smart-fun/elastick/resources/joysticks/amiga_joystick.jpg

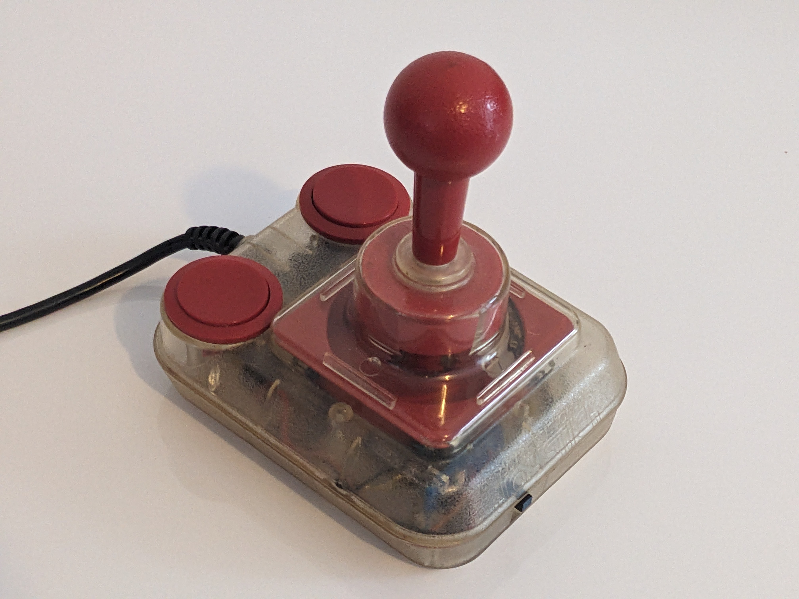
resources/joysticks/amiga_joystick.jpg
