smart-fun/elastick/resources/joysticks/atari_2600_paddles.jpg

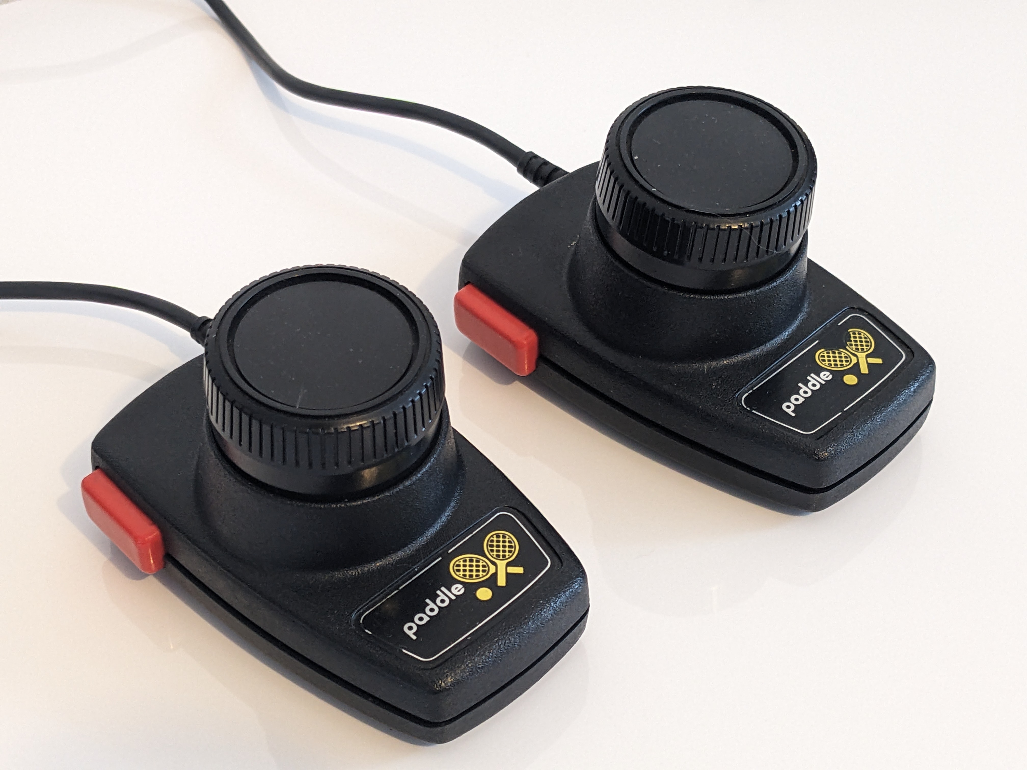
resources/joysticks/atari_2600_paddles.jpg
