smart-fun/elastick/resources/joysticks/coco_deluxe_joystick.jpg

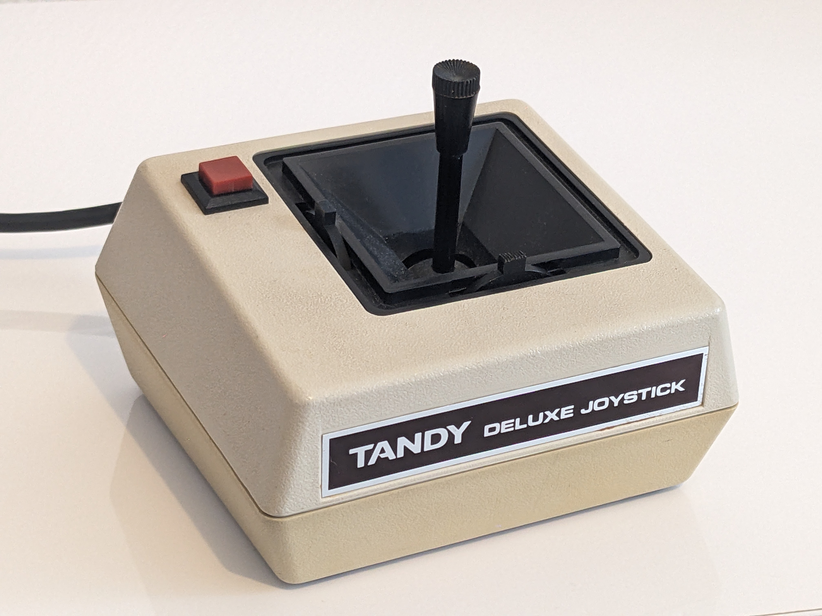
resources/joysticks/coco_deluxe_joystick.jpg
