smart-fun/elastick/resources/joysticks/mega_drive_control_pad.jpg

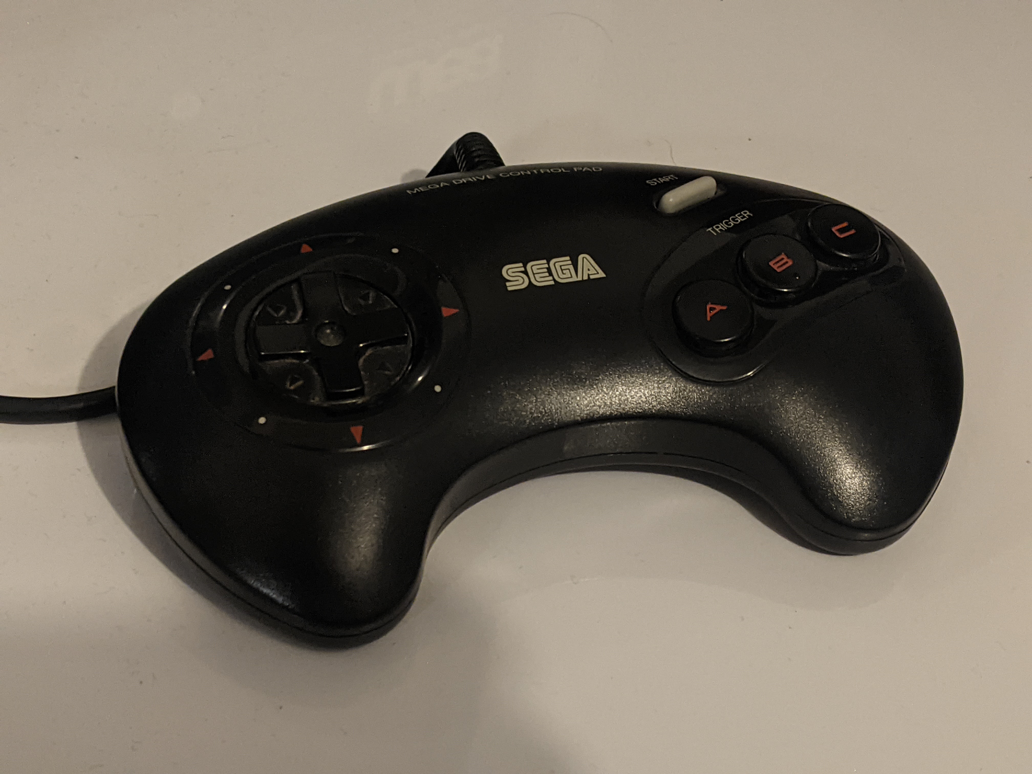
resources/joysticks/mega_drive_control_pad.jpg
