smart-fun/elastick/code/elastick/src/controllers/mega_drive_controller.h

#pragma once
#include "game_controller.h"

class MegaDriveController : public DigitalGameController {
public:
    MegaDriveController();
    uint8_t getNbButtons() override { return 4; };
    void init() override;
    void update() override;
    bool initDetection() override { return false; };
    float readAxis(uint8_t axisNumber) override;
    uint8_t readButton(uint8_t buttonNumber) override;
private:
    std::vector<PinConfig> mappingARules;
    std::vector<PinConfig> mappingBRules;
    bool buttonUp = false;
    bool buttonDown = false;
    bool buttonLeft = false;
    bool buttonRight = false;
    bool buttonA = false;
    bool buttonB = false;
    bool buttonC = false;
    bool buttonStart = false;
};
