smart-fun/elastick/code/elastick/src/menus/ControllersMenu.h

#pragma once

#include "ListMenu.h"
#include "ControllerCategory.h"

class ControllersMenu : public ListMenu {
public:
    ControllersMenu(ControllerCategory controllerCategory);
private:
    ControllerCategory controllerCategory;
};
