smart-fun/elastick/code/elastick/src/controllers/atari_mouse_controller.h

#pragma once
#include "mouse_controller.h"

class AtariMouseController : public MouseController {
public:
    AtariMouseController();
    void init() override;
    void deinit() override;
    void update() override;
protected:
    void getMouseDirectionPins(uint8_t &x1Pin, uint8_t &x2Pin, uint8_t &y1Pin, uint8_t &y2Pin) override;
    void getMouseButtonPins(uint8_t &button1Pin, uint8_t &button2Pin, uint8_t &button3Pin) override;
};
