smart-fun/elastick/code/elastick/src/menus/ListMenu.cpp

#include "ListMenu.h"
#include "DisplayManager.h"
#include "game_controllers.h"
#include "MenuController.h"

MenuItem::MenuItem(MenuItemType type, const char *displayText)
{
    this->type = type;
    this->displayText = displayText;
}

MenuItem::MenuItem(MenuAction menuAction, const char *displayText)
    : MenuItem(MenuItemType::Action, displayText)
{
    data.menuAction = menuAction;
}

MenuItem::MenuItem(ControllerCategory controllerCategory, const char *displayText)
    : MenuItem(MenuItemType::Category, displayText)
{
    data.controllerCategory = controllerCategory;
}

MenuItem::MenuItem(GameController *controller, const char *displayText)
    : MenuItem(MenuItemType::Controller, displayText)
{
    data.controller = controller;
}

ListMenu::ListMenu()
{
}

void ListMenu::show()
{
    DisplayManager::getInstance().showList(getTitle(), list, selectedIndex);
}

void ListMenu::update()
{
    // nothing to do so far
}

void ListMenu::onPrevious()
{
    if (selectedIndex > 0)
    {
        --selectedIndex;
    }
    show();
}

void ListMenu::onNext()
{
    if (selectedIndex < list.size() - 1)
    {
        ++selectedIndex;
    }
    show();
}

// TODO: call controller->deinit() when going back to Joystick/Mouse/Paddle Menus (from Test or Play)
void ListMenu::onValidate()
{
    MenuItem *menuItem = list[selectedIndex];
    switch (menuItem->type)
    {
    case MenuItemType::Action:
    {
        MenuAction menuAction = menuItem->data.menuAction;
        if (menuAction == MenuAction::BACK_TO_CATEGORY_MENU)
        {
            MenuController::getInstance().setCurrentMenu(MenuController::MenuID::Category);
        }
        else if (menuAction == MenuAction::BACK_TO_CONTROLLERS_MENU)
        {
            GameController *controller = GameControllers::getInstance().getSelectedController();
            controller->deinit();
            ControllerCategory category = controller->getCategory();
            startControllersMenu(category);
        }
        else if (menuAction == MenuAction::PLAY)
        {
            GameController *controller = GameControllers::getInstance().getSelectedController();
            controller->init();
            MenuController::getInstance().setCurrentMenu(MenuController::MenuID::Play);
        }
        else if (menuAction == MenuAction::TEST)
        {
            GameController *controller = GameControllers::getInstance().getSelectedController();
            controller->init();
            MenuController::getInstance().setCurrentMenu(MenuController::MenuID::Test);
        }
        break;
    }
    case MenuItemType::Category:
    {
        startControllersMenu(menuItem->data.controllerCategory);
        break;
    }
    case MenuItemType::Controller:
    {
        GameController *controller = menuItem->data.controller;
        GameControllers::getInstance().setSelectedController(controller);
        // selected->init();
        MenuController::getInstance().setCurrentMenu(MenuController::MenuID::Action);
        break;
    }
    }
}

void ListMenu::startControllersMenu(ControllerCategory category)
{
    if (category == ControllerCategory::JOY)
    {
        MenuController::getInstance().setCurrentMenu(MenuController::MenuID::JoystickList);
    }
    else if (category == ControllerCategory::MOUSE)
    {
        MenuController::getInstance().setCurrentMenu(MenuController::MenuID::MouseList);
    }
    else if (category == ControllerCategory::PADDLE)
    {
        MenuController::getInstance().setCurrentMenu(MenuController::MenuID::PaddleList);
    }
}
