smart-fun/elastick/code/elastick/es_display_manager.cpp

#include <Wire.h>
#include "es_display_manager.h"
#include "es_game_controllers.h"
#include "es_game_controller.h"
#include "es_action_menu.h"

DisplayManager& DisplayManager::getInstance() {
    static DisplayManager instance;
    return instance;
}

DisplayManager::DisplayManager() {
    lcd.begin();
    lcd.clearBuffer();
    lcd.sendBuffer();
}

void DisplayManager::init() {
}

void DisplayManager::showWelcome() {
  lcd.clearBuffer();
  lcd.setFont(u8g2_font_DigitalDisco_te);
  printCenterX("ELASTICK ADAPTER", 10);
  lcd.setFont(u8g2_font_ncenB08_tr);
  printCenterXY("Version 0.2");
  lcd.sendBuffer();
}

void DisplayManager::showControllerList(int currentIndex) {
  lcd.clearBuffer();
 
  lcd.setFont(u8g2_font_DigitalDisco_te);
  printCenterX("CONTROLLERS", 10);
  lcd.setFont(u8g2_font_ncenB08_tr);

  GameControllers & gc = GameControllers::getInstance();
  int nbControllers = gc.getCount();
  int x=12;
  int y=24;
  int index = currentIndex % nbControllers;
  int yMax = lcd.getDisplayHeight() + 10;
  lcd.drawStr(0, y, ">");
  do {
    lcd.drawStr(x, y, gc.get(index)->getName());
    y += 12;
    index = (index + 1) % nbControllers;
  } while (y < yMax);

  lcd.sendBuffer();
}

void DisplayManager::showDetecting(GameController * controller) {
  lcd.clearBuffer();
  lcd.setFont(u8g2_font_DigitalDisco_te);
  printCenterX(controller->getName(), 10);
  lcd.setFont(u8g2_font_ncenB08_tr);
  printCenterXY("detecting...");
  lcd.sendBuffer();
}

void DisplayManager::showActions(const char * menuName, std::vector<ActionItem*> & actionItems, int actionIndex) {
  lcd.clearBuffer();
  lcd.setFont(u8g2_font_DigitalDisco_te);
  printCenterX(menuName, 10);
  lcd.setFont(u8g2_font_ncenB08_tr);

  int count = actionItems.size();
  int x=12;
  int y=24;
  int index = actionIndex % count;
  int yMax = lcd.getDisplayHeight() + 10;
  lcd.drawStr(0, y, ">");
  do {
    lcd.drawStr(x, y, actionItems[index]->displayName);
    y += 12;
    index = (index + 1) % count;
  } while (y < yMax);

  lcd.sendBuffer();
}

void DisplayManager::showTest(GameController * controller) {
  lcd.clearBuffer();
  lcd.setFont(u8g2_font_DigitalDisco_te);
  printCenterX("TESTING", 10);
  lcd.setFont(u8g2_font_ncenB08_tr);
  lcd.drawStr(0, 24, ">");
  lcd.drawStr(12, 24, "BACK");

  //lcd.drawBox(0, 32, 32, 32);
  int halfSize = 16;
  int centerX = 64;
  int centerY = 64-halfSize;
  lcd.drawLine(centerX - halfSize, centerY, centerX + halfSize, centerY);
  lcd.drawLine(centerX, centerY - halfSize, centerX, centerY + halfSize);

  float x = controller->readAxis(0);
  float y = controller->readAxis(1);
  uint8_t b1 = controller->readButton(0);
  uint8_t b2 = controller->readButton(1);
  lcd.drawCircle(centerX + (x*halfSize), centerY - (y*halfSize), 3);

  x = 100;
  y = centerY - 10;
  int radius = 5;
  if (b1) {
    lcd.drawDisc(x, y, radius);
  } else {
    lcd.drawCircle(x, y, radius);
  }
  y = centerY + 10;
  if (b2) {
    lcd.drawDisc(x, y, radius);
  } else {
    lcd.drawCircle(x, y, radius);
  }

  lcd.sendBuffer();
}

void DisplayManager::showPlay(bool connected) {
  lcd.clearBuffer();
  lcd.setFont(u8g2_font_DigitalDisco_te);
  printCenterX("PLAYING", 10);
  lcd.setFont(u8g2_font_ncenB08_tr);
  lcd.drawStr(0, 24, ">");
  lcd.drawStr(12, 24, "BACK");

  uint8_t y = 48;
  if (connected) {
    printCenterX("BT Connected!", y);
  } else {
    printCenterX("Bluetooth connection...", y);
  }

  lcd.sendBuffer();
}

void DisplayManager::printCenterX(const char * text, int y) {
  u8g2_uint_t screenWidth = lcd.getDisplayWidth();
  u8g2_uint_t textWidth = lcd.getStrWidth(text);
  u8g2_uint_t x = (screenWidth - textWidth) / 2;
  lcd.drawStr(x, y, text);
}

void DisplayManager::printCenterXY(const char * text) {
  u8g2_uint_t screenHeight = lcd.getDisplayHeight();
  u8g2_uint_t textHeight = lcd.getMaxCharHeight();
  u8g2_uint_t y = (screenHeight + textHeight) / 2;
  printCenterX(text, y);
}
