smart-fun/elastick/code/elastick/src/menus/PlayMenu.h

#pragma once
#include "BaseMenu.h"

class PlayMenu : public BaseMenu {
public:
    PlayMenu();
    void init() override;
    void deinit() override;
    void show() override;
    void update() override;
    void onPrevious() override;
    void onNext() override;
    void onValidate() override;
private:
    void sendBatteryPercent();
    bool isConnected = false;
};
