smart-fun/elastick/code/elastick/src/menus/JoystickMenu.cpp

#include <Arduino.h>
#include "JoystickMenu.h"

JoystickMenu::JoystickMenu()
    :ControllersMenu(ControllerCategory::JOY) {
    Serial.println("JoystickMenu created");
}

const char * JoystickMenu::getTitle() {
    return "STICKS & PADS";
}
