smart-fun/elastick/code/elastick/src/menus/MouseMenu.cpp

#include <Arduino.h>
#include "MouseMenu.h"

MouseMenu::MouseMenu()
    :ControllersMenu(ControllerCategory::MOUSE) {
    Serial.println("MouseMenu created");
}

const char * MouseMenu::getTitle() {
    return "MOUSES";
}
