smart-fun/elastick/code/elastick/src/menus/PaddleMenu.cpp

#include <Arduino.h>
#include "PaddleMenu.h"

PaddleMenu::PaddleMenu()
    :ControllersMenu(ControllerCategory::PADDLE) {
    Serial.println("PaddleMenu created");
}

const char * PaddleMenu::getTitle() {
    return "PADDLES";
}
