smart-fun/elastick/code/elastick/src/menus/TestMenu.cpp

#include <Arduino.h>
#include "TestMenu.h"
#include "DisplayManager.h"
#include "MenuController.h"
#include "game_controllers.h"
#include "game_controller.h"

TestMenu::TestMenu() {
  Serial.println("TestMenu created");
}

void TestMenu::show() {
  GameController * selected = GameControllers::getInstance().getSelectedController();
  DisplayManager::getInstance().showTest(selected);
}

void TestMenu::update() {
  GameController * selected = GameControllers::getInstance().getSelectedController();
  selected->update();
  show();
}

void TestMenu::onPrevious() {
    // nothing to do
}

void TestMenu::onNext() {
    // nothing to do
}

void TestMenu::onValidate() {
    MenuController::getInstance().setCurrentMenu(MenuController::MenuID::Action);
}
