smart-fun/elastick/code/elastick/es_test_menu.h

#pragma once
#include "es_base_menu.h"

class TestMenu : public BaseMenu {
public:
    TestMenu();
    void show() override;
    void update() override;
    void onNext() override;
    void onValidate() override;
};
